PonderSlime/Pyp-Boy/Pyp-Boy CAD Models/PyP-Boy Finished CAD Files/Part Studio 1 - Arm Front.step

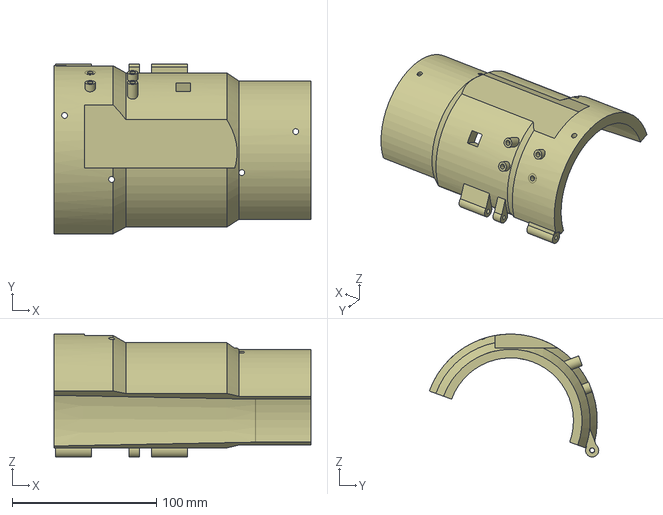
[picture p14: CAD file, 2025-07-18]
Pyp-Boy CAD Models/PyP-Boy Finished CAD Files/Part Studio 1 - Arm Front.step
178.0 x 117.4 x 85.1 mm
