PonderSlime/Pyp-Boy/Pyp-Boy CAD Models/PyP-Boy Finished CAD Files/Part Studio 1 - Electronic Housing.step

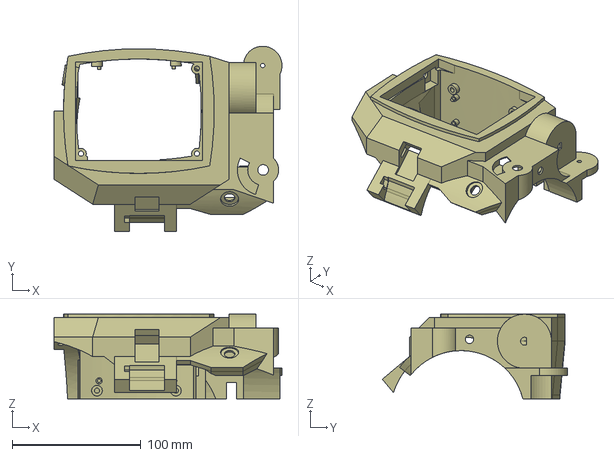
[picture p15: CAD file, 2025-07-18]
Pyp-Boy CAD Models/PyP-Boy Finished CAD Files/Part Studio 1 - Electronic Housing.step
176.9 x 143.9 x 65.7 mm
