PonderSlime/Pyp-Boy/Pyp-Boy CAD Models/PyP-Boy Finished CAD Files/Part Studio 1 - Electronic Housing Rear Plate.step

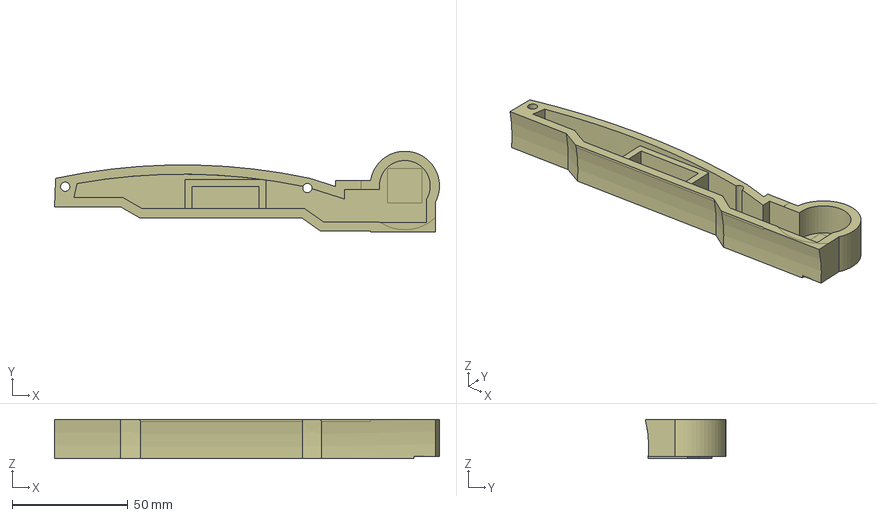
[picture p16: CAD file, 2025-07-18]
Pyp-Boy CAD Models/PyP-Boy Finished CAD Files/Part Studio 1 - Electronic Housing Rear Plate.step
166.6 x 34.8 x 17.0 mm
