PonderSlime/Pyp-Boy/Pyp-Boy CAD Models/PyP-Boy Finished CAD Files/Part Studio 1 - Screen Front Cover.step

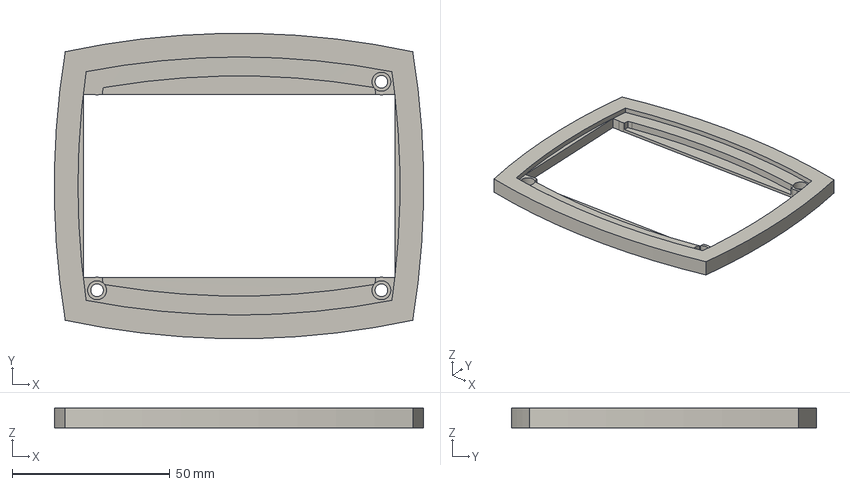
[picture p17: CAD file, 2025-07-18]
Pyp-Boy CAD Models/PyP-Boy Finished CAD Files/Part Studio 1 - Screen Front Cover.step
116.8 x 96.5 x 6.26 mm
