PonderSlime/Pyp-Boy/Pip Boy wiring/Pip Boy wiring.kicad_sch

## KiCad design Pip Boy wiring/Pip Boy wiring.kicad_sch (2025-07-19, an earlier design)

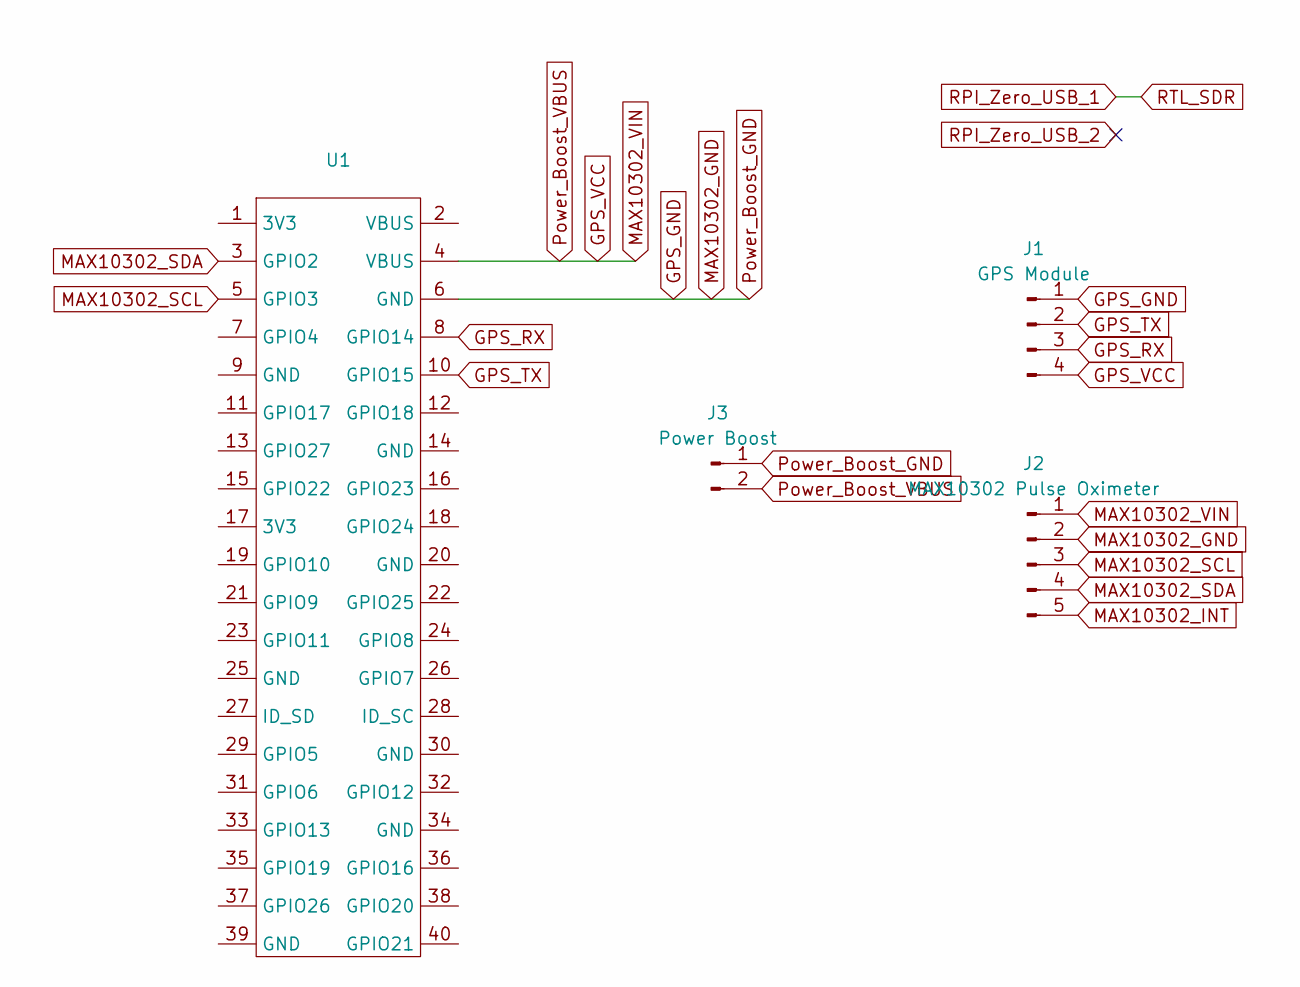
[picture p18: schematic Pip Boy wiring.kicad_sch]

Parts:
J1: GPS Module
J2: MAX10302 Pulse Oximeter
J3: Power Boost
U1: RPI Zero Footprint

Connections:
GPS_GND: J1.1, J2.2, J3.1, U1.6 (GND)
GPS_RX: J1.3, U1.8 (GPIO14)
GPS_TX: J1.2, U1.10 (GPIO15)
GPS_VCC: J1.4, J2.1, J3.2, U1.4 (VBUS)
MAX10302_INT: J2.5
MAX10302_SCL: J2.3, U1.5 (GPIO3)
MAX10302_SDA: J2.4, U1.3 (GPIO2)
